DasPocky/3D-Druck-Modelle/FutterStorage/paket/bilder/15-vollausbau.png

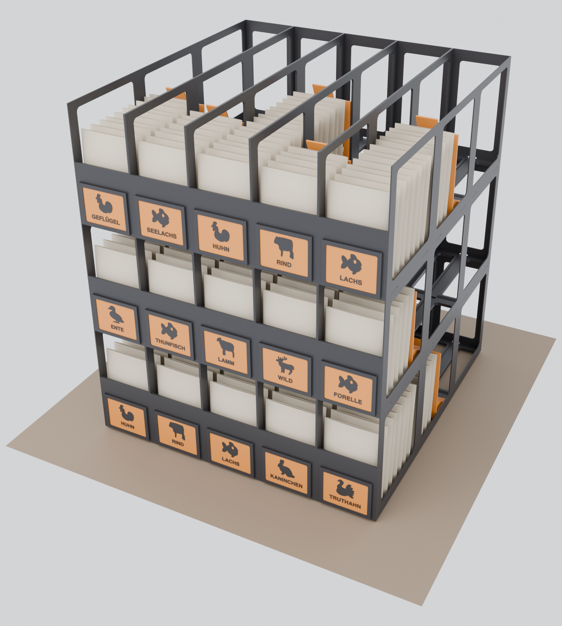
FutterStorage/paket/bilder/15-vollausbau.png
