DasPocky/3D-Druck-Modelle/FutterStorage/bilder/b_end.png

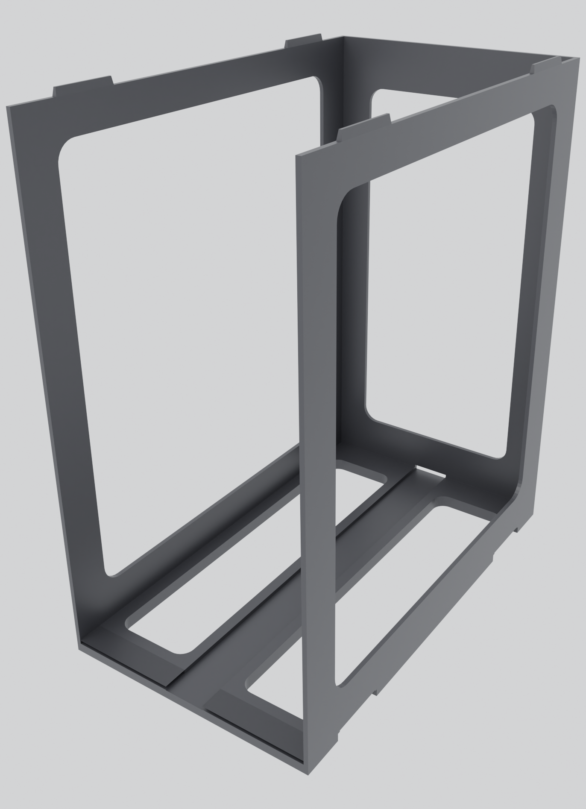
FutterStorage/bilder/b_end.png
