DasPocky/3D-Druck-Modelle/FutterStorage/bilder/b_explosion.png

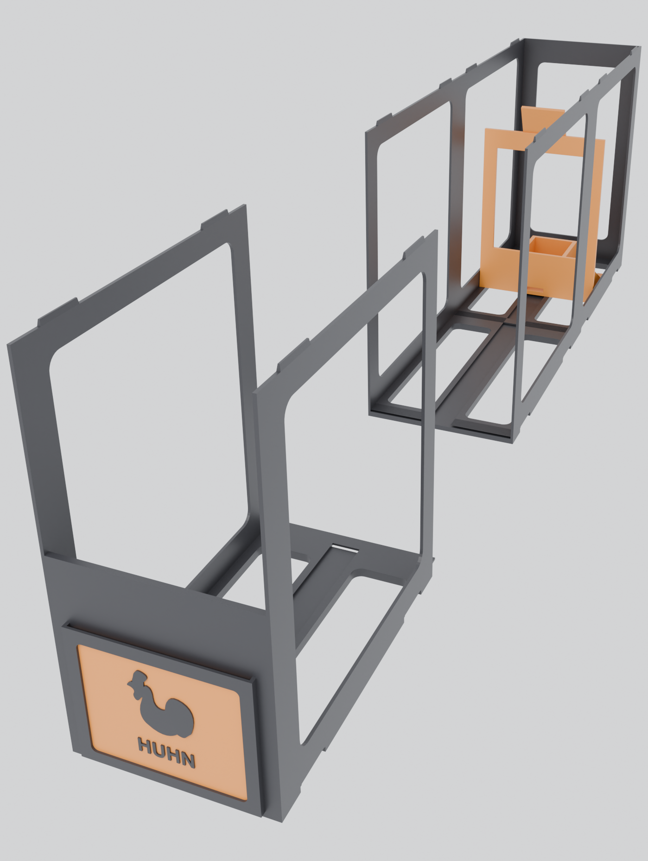
FutterStorage/bilder/b_explosion.png
