DasPocky/3D-Druck-Modelle/FutterStorage/bilder/b_front.png

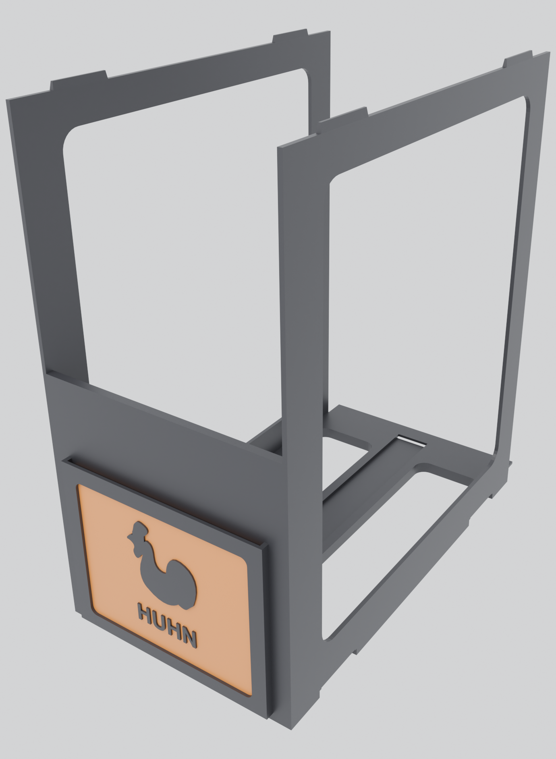
FutterStorage/bilder/b_front.png
