DasPocky/3D-Druck-Modelle/FutterStorage/bilder/b_greifraum.png

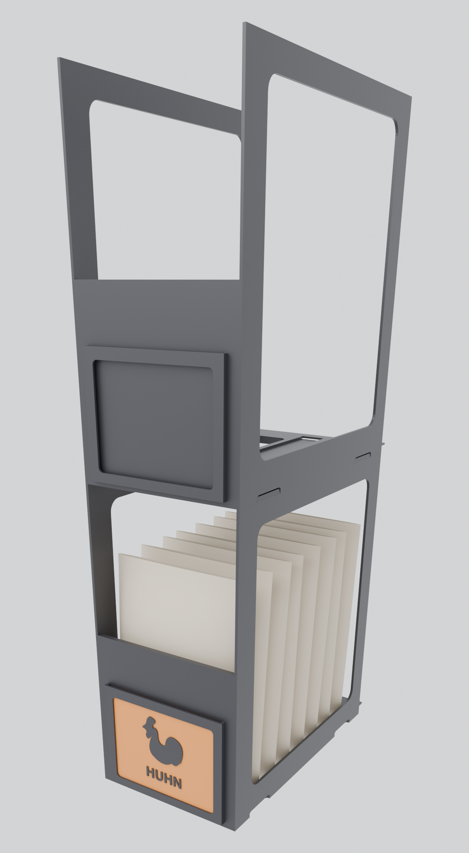
FutterStorage/bilder/b_greifraum.png
