DasPocky/3D-Druck-Modelle/FutterStorage/bilder/b_mitte.png

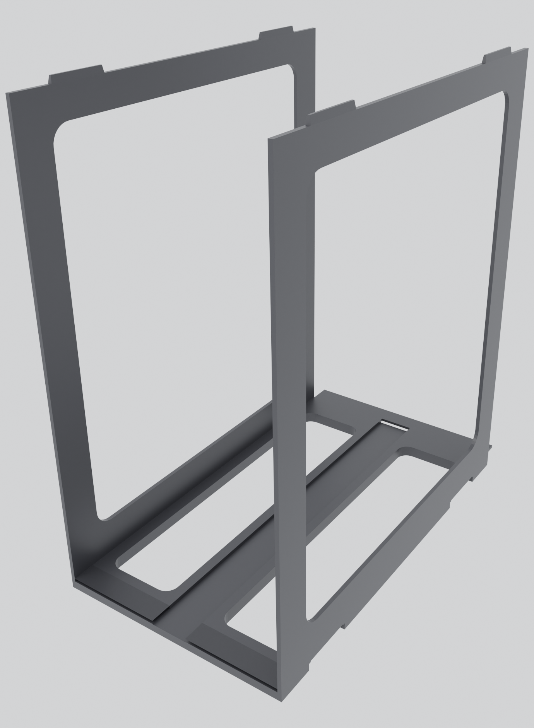
FutterStorage/bilder/b_mitte.png
