DasPocky/3D-Druck-Modelle/FutterStorage/bilder/b_schild.png

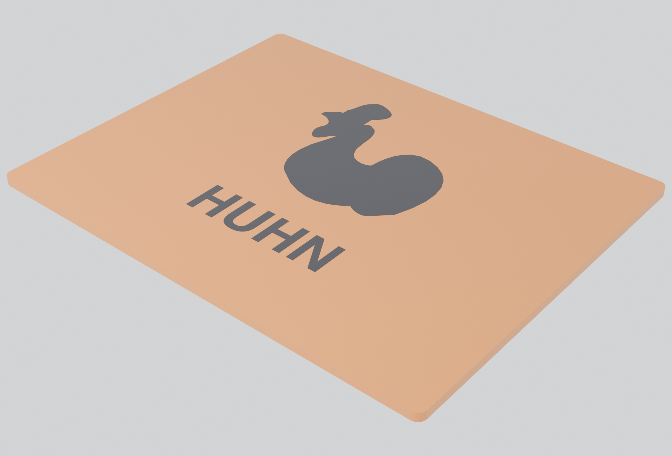
FutterStorage/bilder/b_schild.png
