DasPocky/3D-Druck-Modelle/FutterStorage/bilder/b_wanne.png

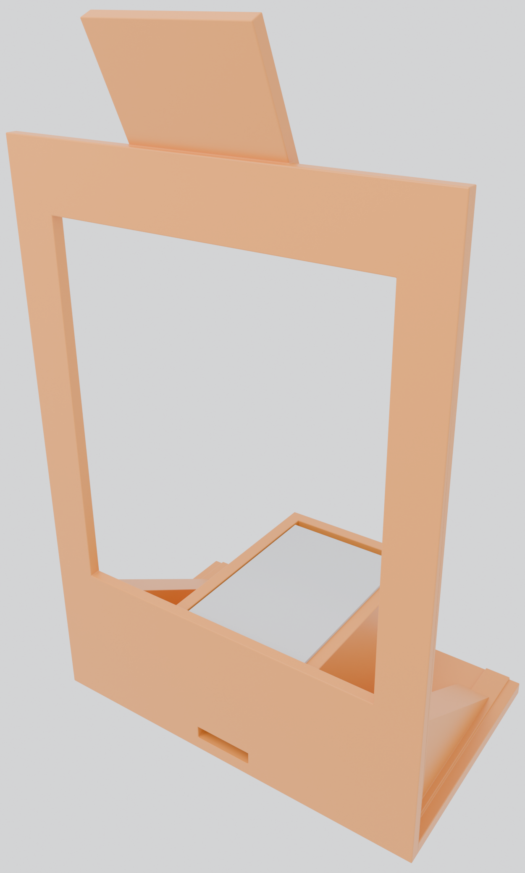
FutterStorage/bilder/b_wanne.png
