DasPocky/3D-Druck-Modelle/FutterStorage/bilder/schilder/01-huhn.png

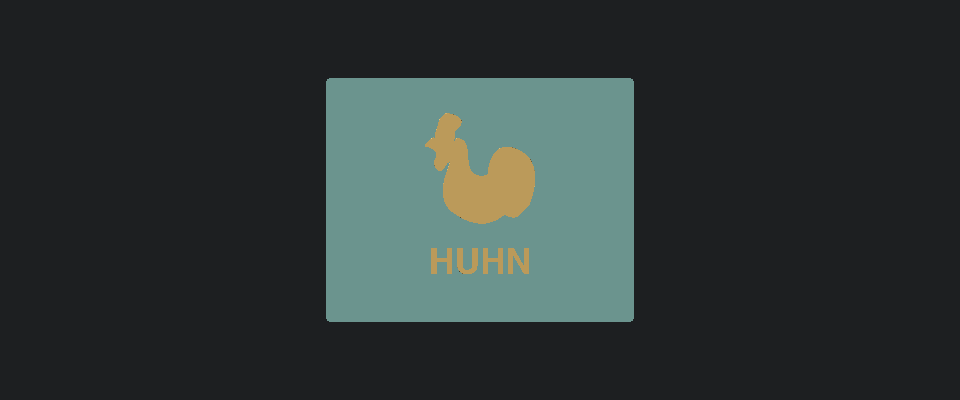
FutterStorage/bilder/schilder/01-huhn.png
