DasPocky/3D-Druck-Modelle/FutterStorage/paket/bilder/12-varianten-ebene.png

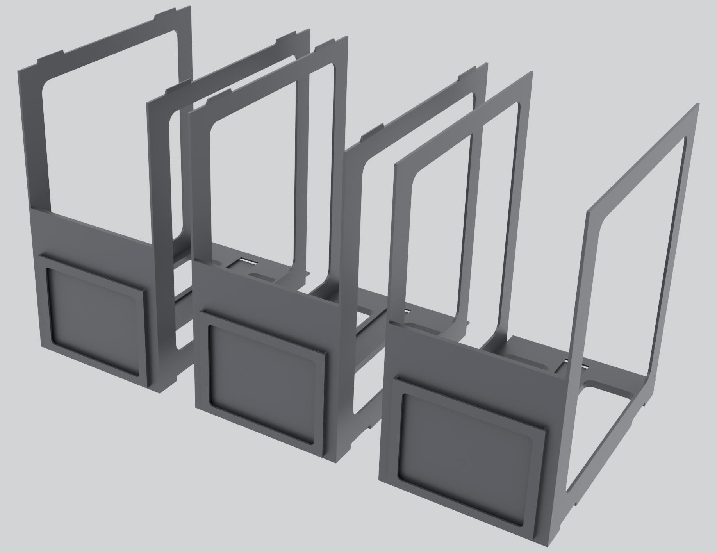
FutterStorage/paket/bilder/12-varianten-ebene.png
