DasPocky/3D-Druck-Modelle/FutterStorage/paket/bilder/14-eine-ebene.png

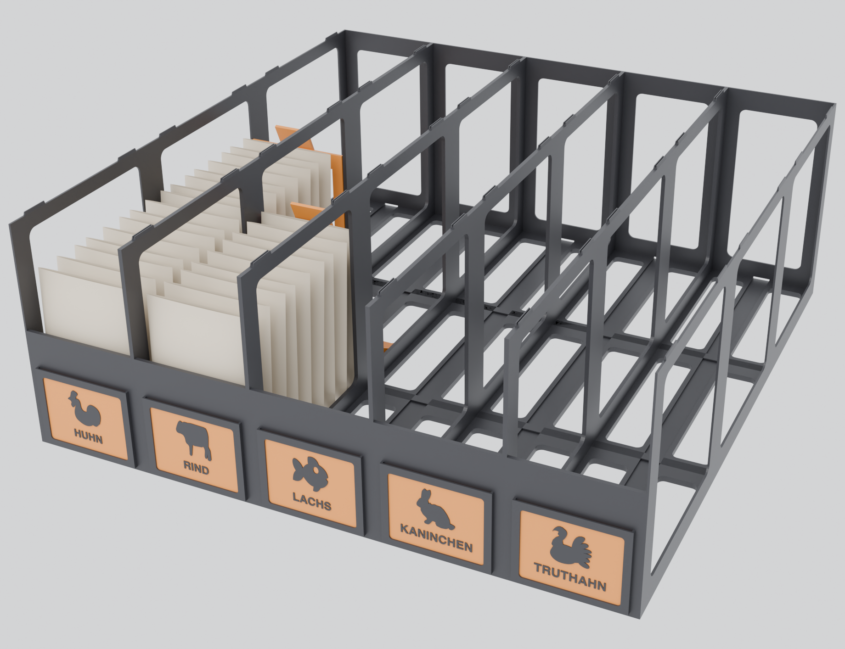
FutterStorage/paket/bilder/14-eine-ebene.png
