DasPocky/3D-Druck-Modelle/FutterStorage/stl/segmente/front-oben-links.stl

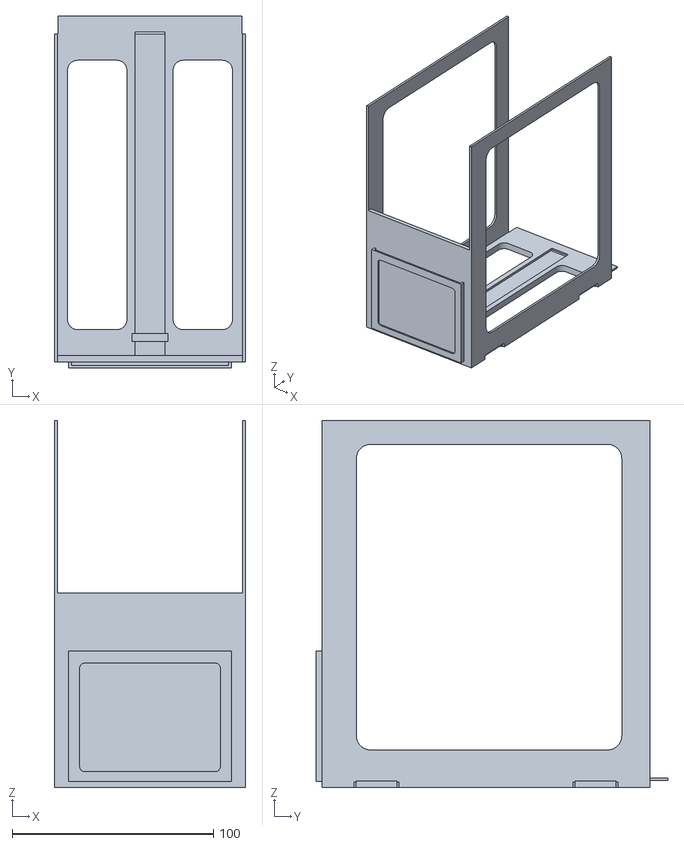
[picture p27: CAD file, 2026-08-01]
FutterStorage/stl/segmente/front-oben-links.stl
95.2 x 175.1 x 182.8
