DasPocky/3D-Druck-Modelle/FutterStorage/stl/segmente/end-oben-links.stl

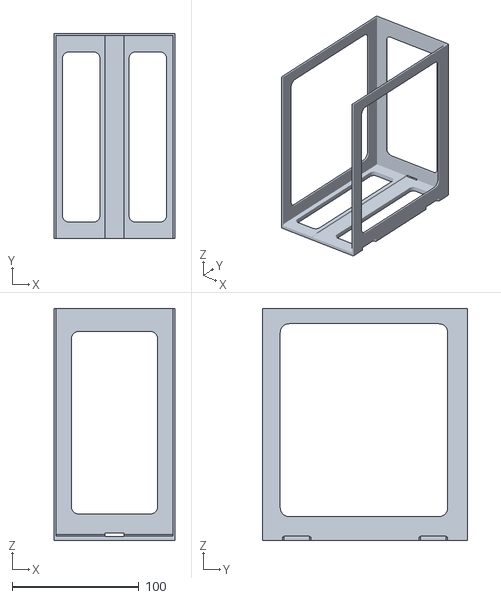
[picture p28: CAD file, 2026-08-01]
FutterStorage/stl/segmente/end-oben-links.stl
95.2 x 161.6 x 182.8
