DasPocky/3D-Druck-Modelle/FutterStorage/paket/stl/schilder/10-forelle-text.stl

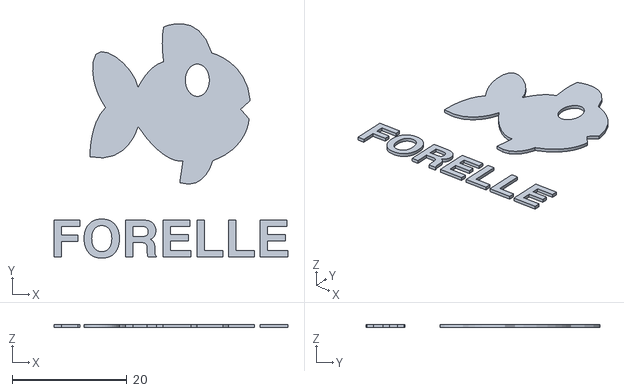
[picture p29: CAD file, 2026-08-01]
FutterStorage/paket/stl/schilder/10-forelle-text.stl
40.9 x 40.9 x 0.6
