DasPocky/3D-Druck-Modelle/FutterStorage/paket/stl/verbinder.stl

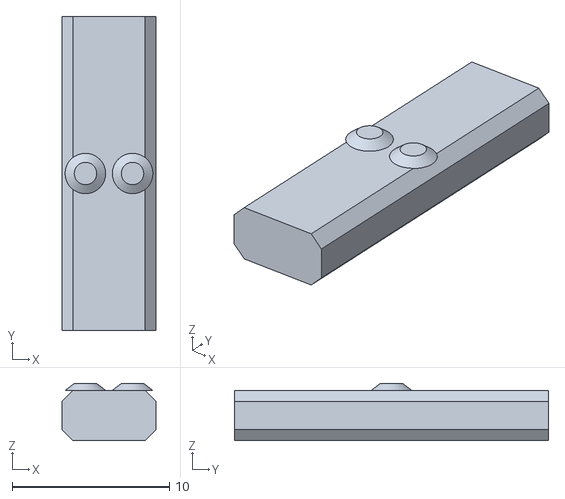
[picture p30: CAD file, 2026-08-01]
FutterStorage/paket/stl/verbinder.stl
6.00 x 20.0 x 3.64
