DasPocky/3D-Druck-Modelle/FutterStorage/stl/schilder/12-fisch-text.stl

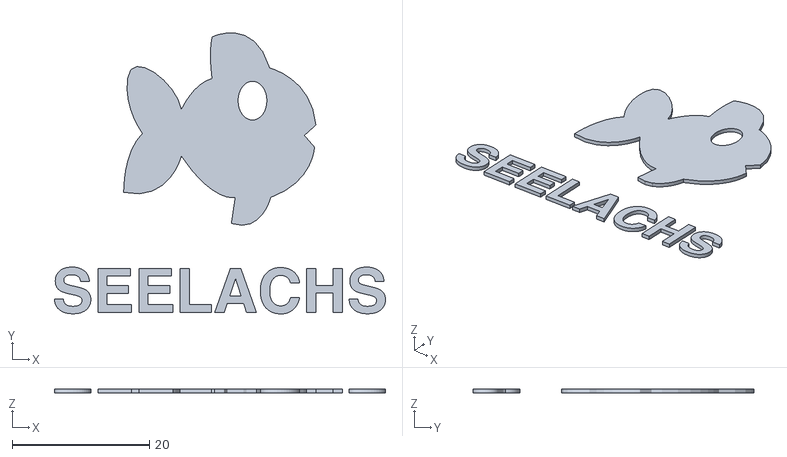
[picture p31: CAD file, 2026-08-01]
FutterStorage/stl/schilder/12-fisch-text.stl
48.2 x 40.9 x 0.6
