DasPocky/3D-Druck-Modelle/FutterStorage/paket/stl/segment-end.stl

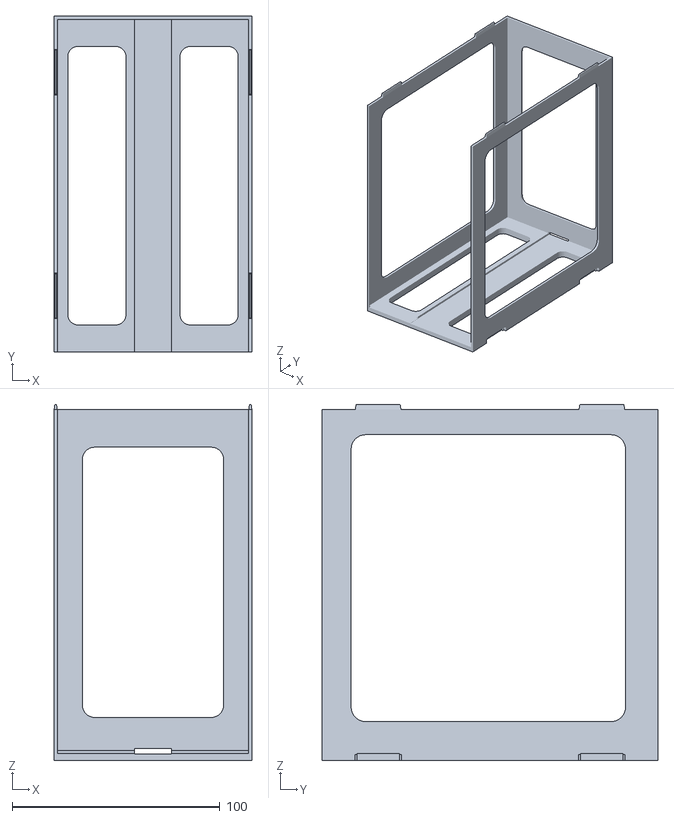
[picture p32: CAD file, 2026-08-01]
FutterStorage/paket/stl/segment-end.stl
95.2 x 161.6 x 171.4
