DasPocky/3D-Druck-Modelle/FutterStorage/stl/segmente/front-unten-links.stl

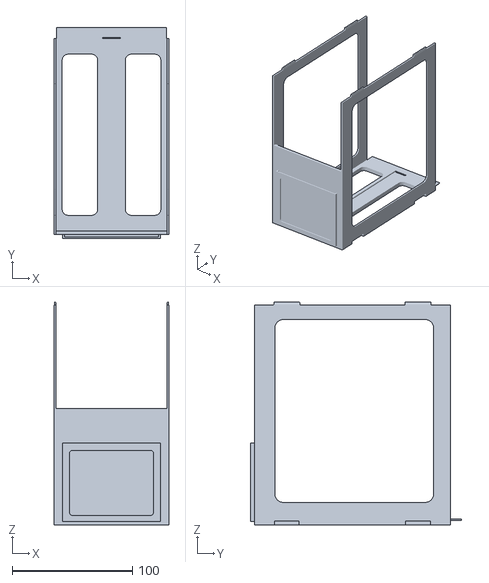
[picture p33: CAD file, 2026-08-01]
FutterStorage/stl/segmente/front-unten-links.stl
95.2 x 175.1 x 185.4
