DasPocky/3D-Druck-Modelle/FutterStorage/paket/stl/segment-front.stl

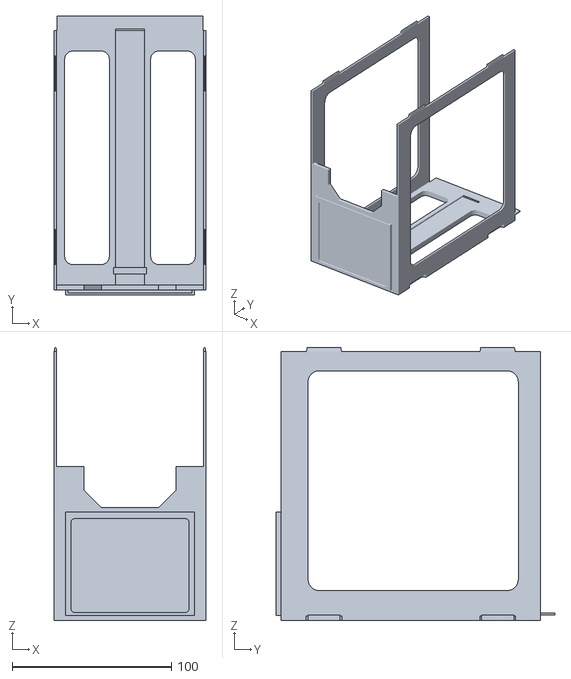
[picture p34: CAD file, 2026-08-01]
FutterStorage/paket/stl/segment-front.stl
95.2 x 175.1 x 171.4
