DasPocky/3D-Druck-Modelle/FutterStorage/stl/segmente/end-unten-links.stl

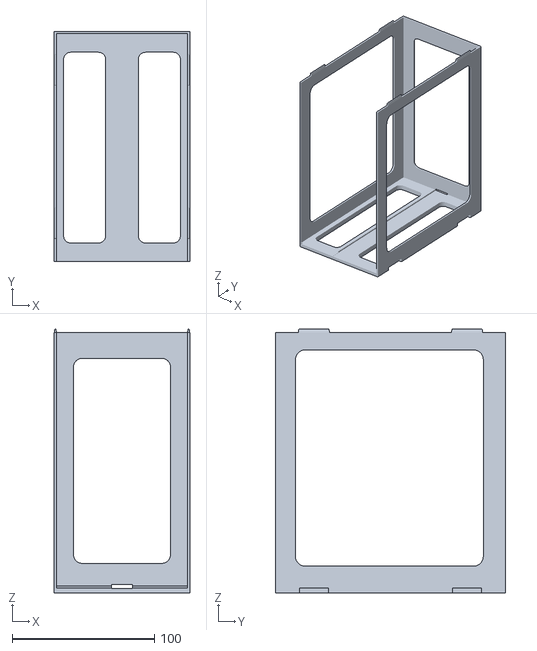
[picture p35: CAD file, 2026-08-01]
FutterStorage/stl/segmente/end-unten-links.stl
95.2 x 161.6 x 185.4
