DasPocky/3D-Druck-Modelle/FutterStorage/paket/stl/schilder/04-kaninchen-text.stl

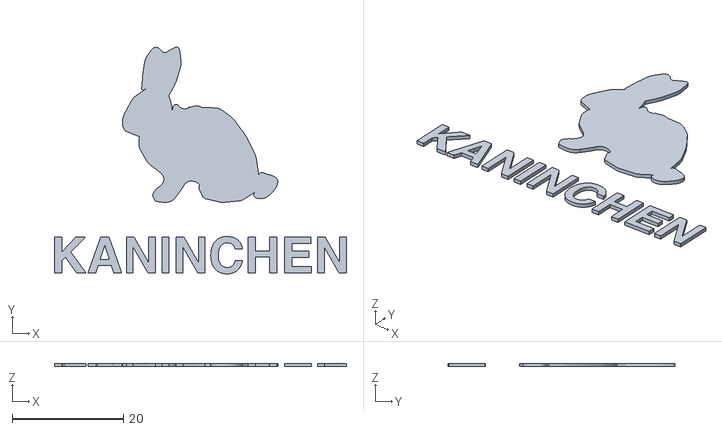
[picture p36: CAD file, 2026-08-01]
FutterStorage/paket/stl/schilder/04-kaninchen-text.stl
52.6 x 40.9 x 0.6
