DasPocky/3D-Druck-Modelle/FutterStorage/paket/stl/segment-mitte.stl

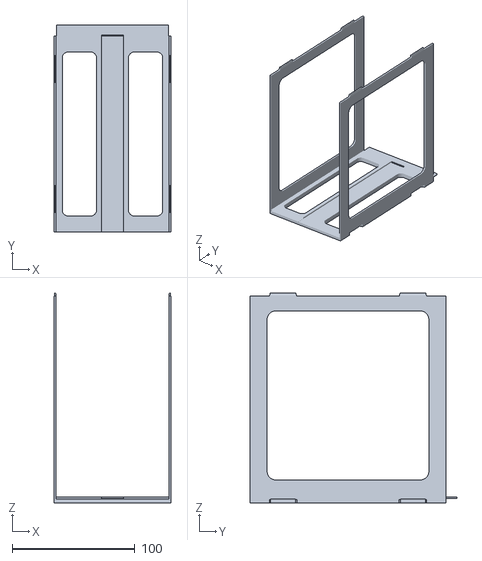
[picture p37: CAD file, 2026-08-01]
FutterStorage/paket/stl/segment-mitte.stl
95.2 x 169.0 x 171.4
