DasPocky/3D-Druck-Modelle/FutterStorage/paket/stl/schilder/07-thunfisch-text.stl

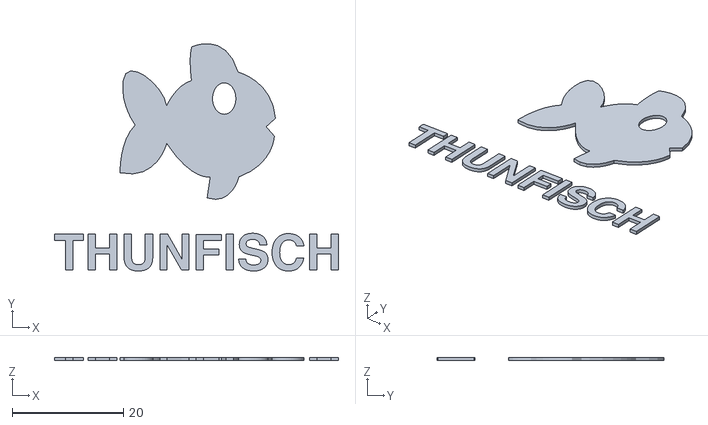
[picture p38: CAD file, 2026-08-01]
FutterStorage/paket/stl/schilder/07-thunfisch-text.stl
51.1 x 40.9 x 0.6
