DasPocky/3D-Druck-Modelle/FutterStorage/paket/stl/schilder/03-lachs-text.stl

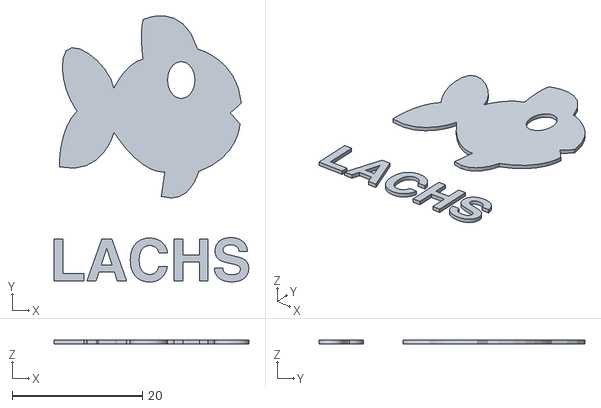
[picture p39: CAD file, 2026-08-01]
FutterStorage/paket/stl/schilder/03-lachs-text.stl
29.9 x 40.9 x 0.6
