DasPocky/3D-Druck-Modelle/FutterStorage/stl/schilder/08-lamm-text.stl

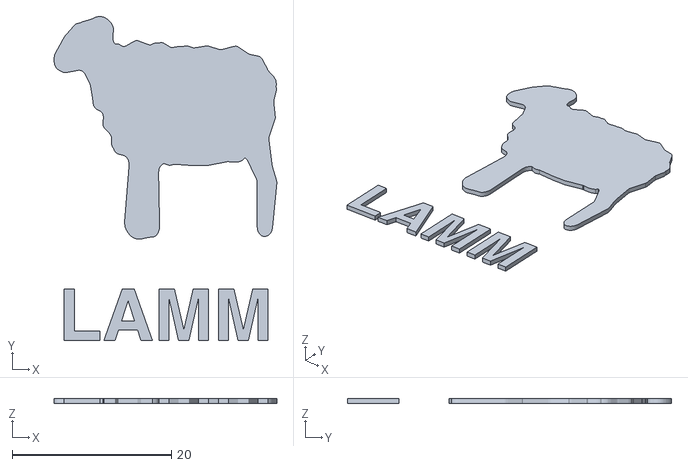
[picture p40: CAD file, 2026-08-01]
FutterStorage/stl/schilder/08-lamm-text.stl
28.0 x 40.7 x 0.6
