DasPocky/3D-Druck-Modelle/FutterStorage/paket/stl/schilder/05-truthahn-text.stl

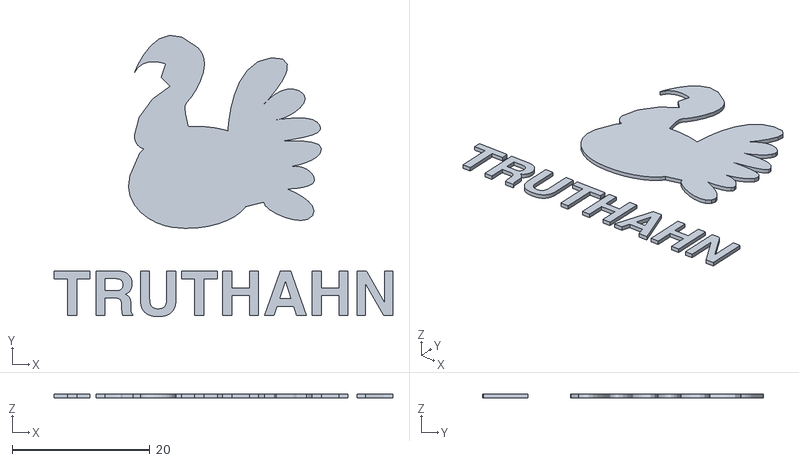
[picture p41: CAD file, 2026-08-01]
FutterStorage/paket/stl/schilder/05-truthahn-text.stl
49.2 x 40.8 x 0.6
